nplan/HomeButtons/docs/assets/hb_promo_1.jpeg

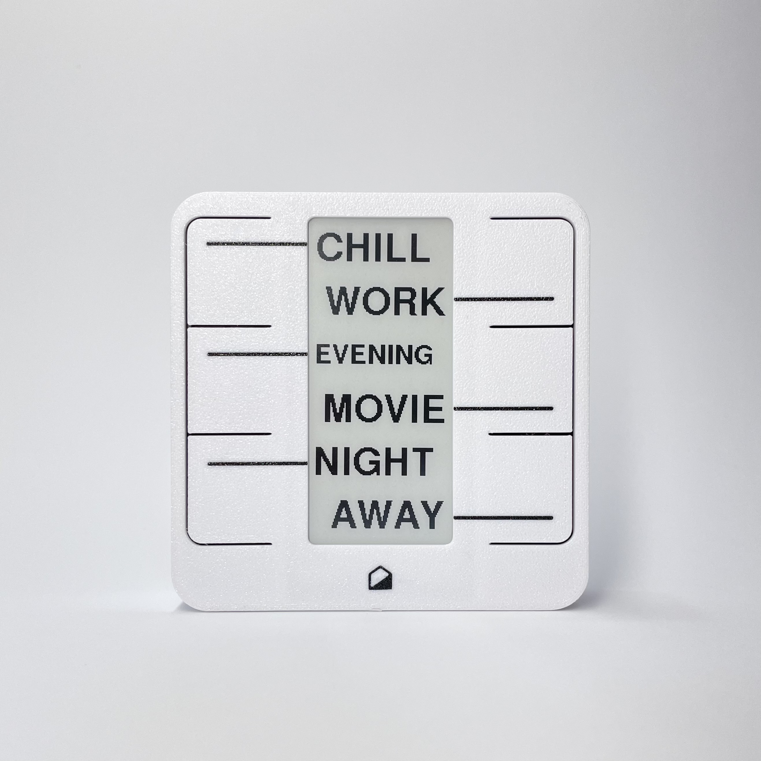
docs/assets/hb_promo_1.jpeg
