nplan/HomeButtons/docs/assets/original_click.gif

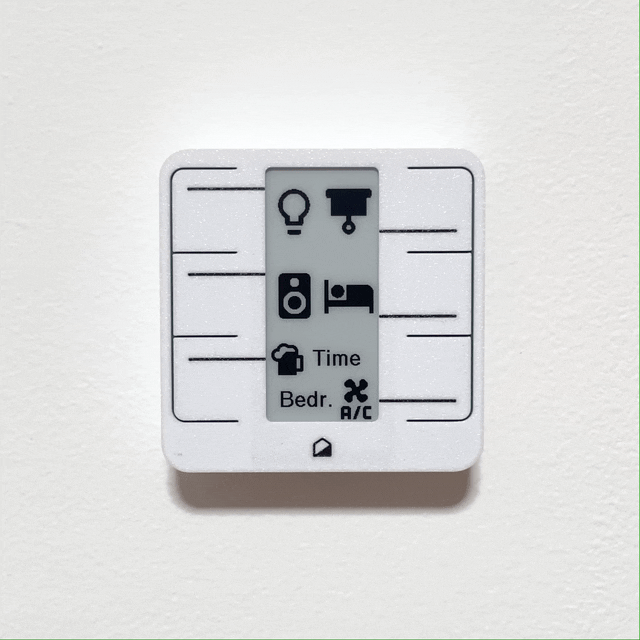
docs/assets/original_click.gif
