nplan/HomeButtons/docs/industrial/assets/button_press.gif

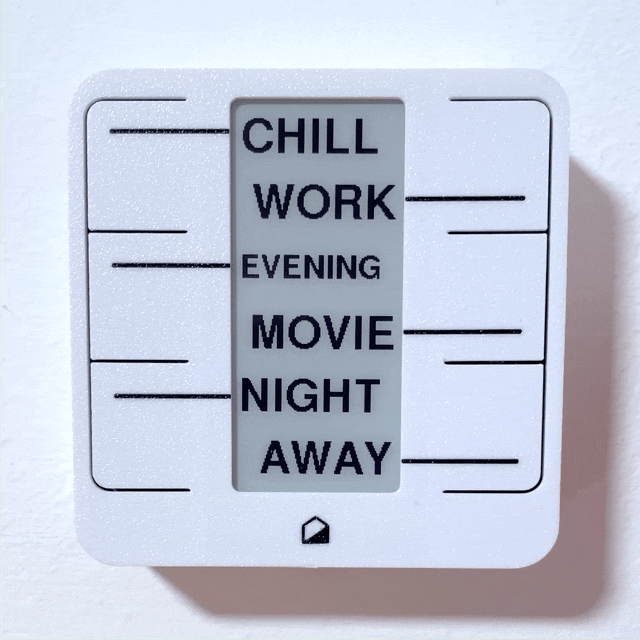
docs/industrial/assets/button_press.gif
