nplan/HomeButtons/docs/industrial/assets/hb_ind_front_iso.png

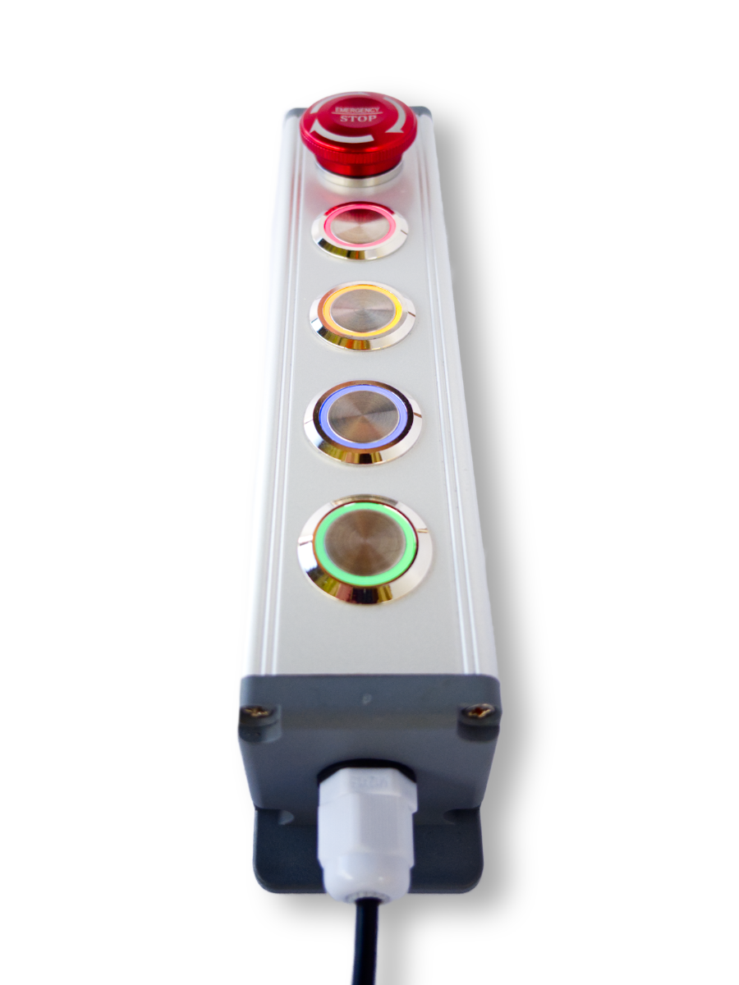
docs/industrial/assets/hb_ind_front_iso.png
