nplan/HomeButtons/docs/industrial/assets/hb_ind_iso.png

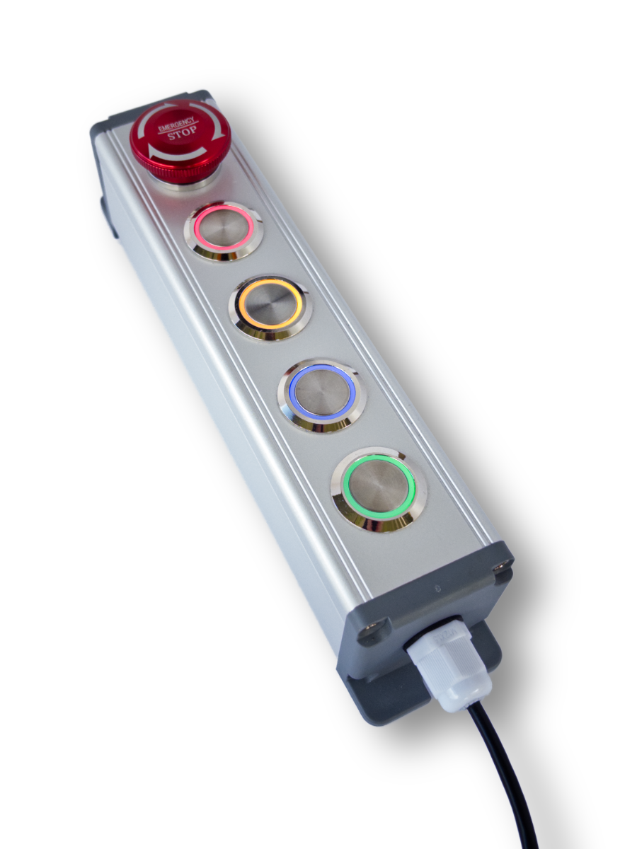
docs/industrial/assets/hb_ind_iso.png
