nplan/HomeButtons/docs/industrial/assets/hb_ind_killswitch_closeup.png

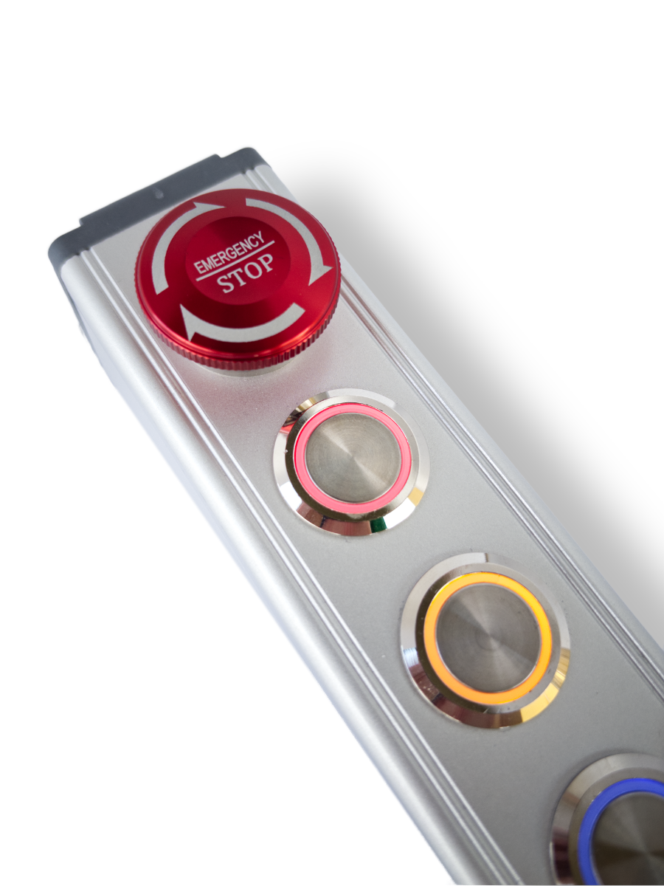
docs/industrial/assets/hb_ind_killswitch_closeup.png
