nplan/HomeButtons/docs/industrial/assets/hb_ind_usb_conn.png

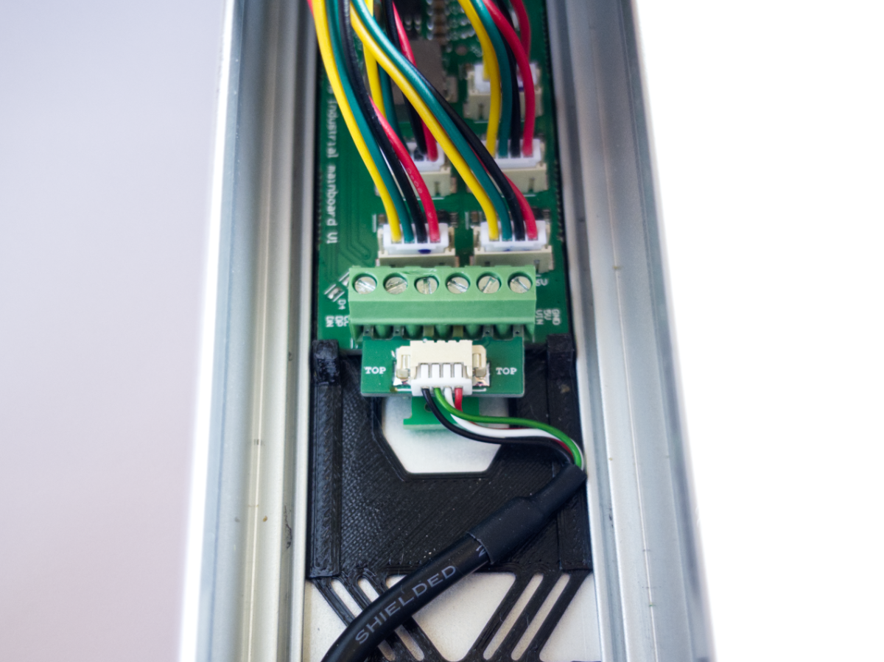
docs/industrial/assets/hb_ind_usb_conn.png
