nplan/HomeButtons/docs/industrial/assets/hb_ind_w_cable.png

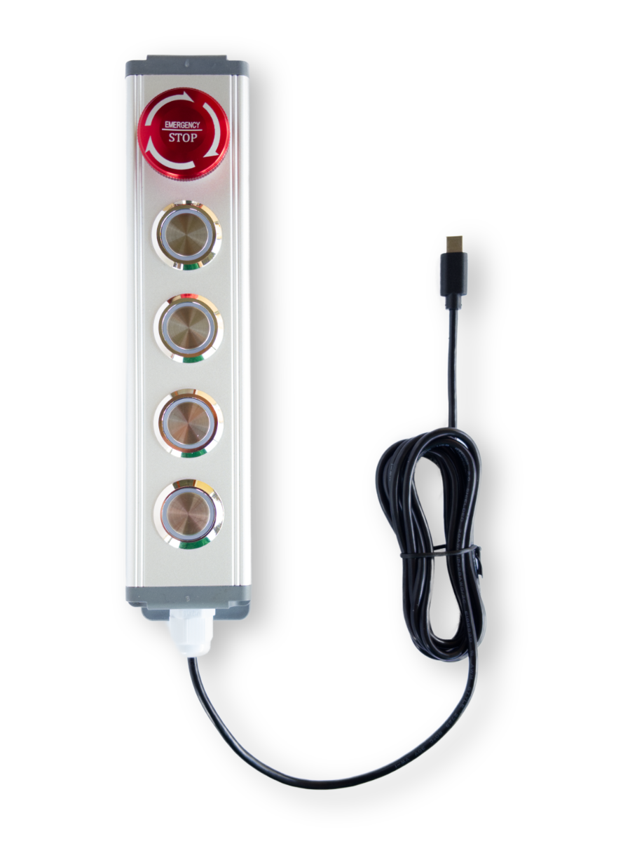
docs/industrial/assets/hb_ind_w_cable.png
