nplan/HomeButtons/docs/industrial/assets/home_buttons_front.jpg

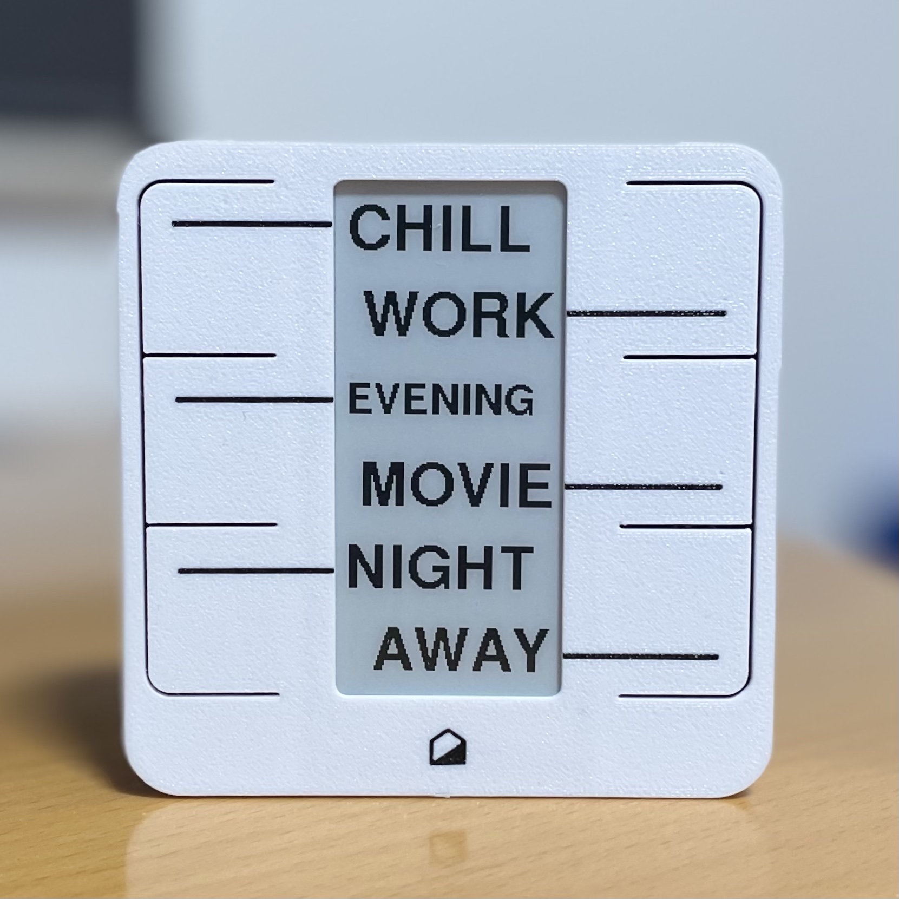
docs/industrial/assets/home_buttons_front.jpg
