nplan/HomeButtons/docs/industrial/assets/mount_2_wall.jpeg

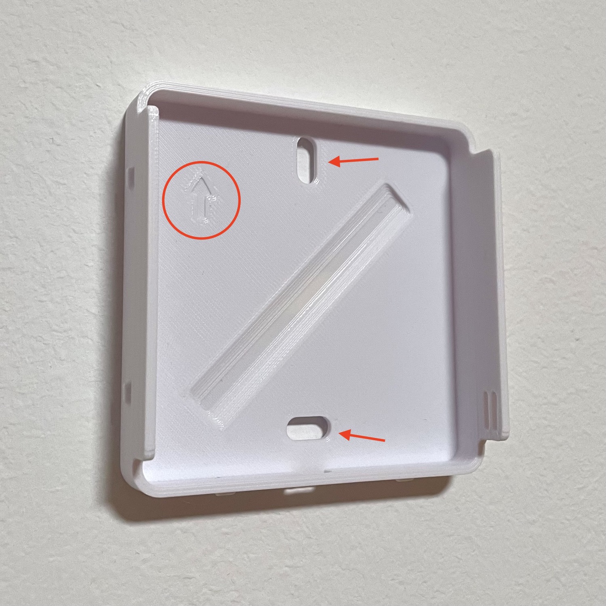
docs/industrial/assets/mount_2_wall.jpeg
