nplan/HomeButtons/docs/industrial/assets/pcb_drawing.png

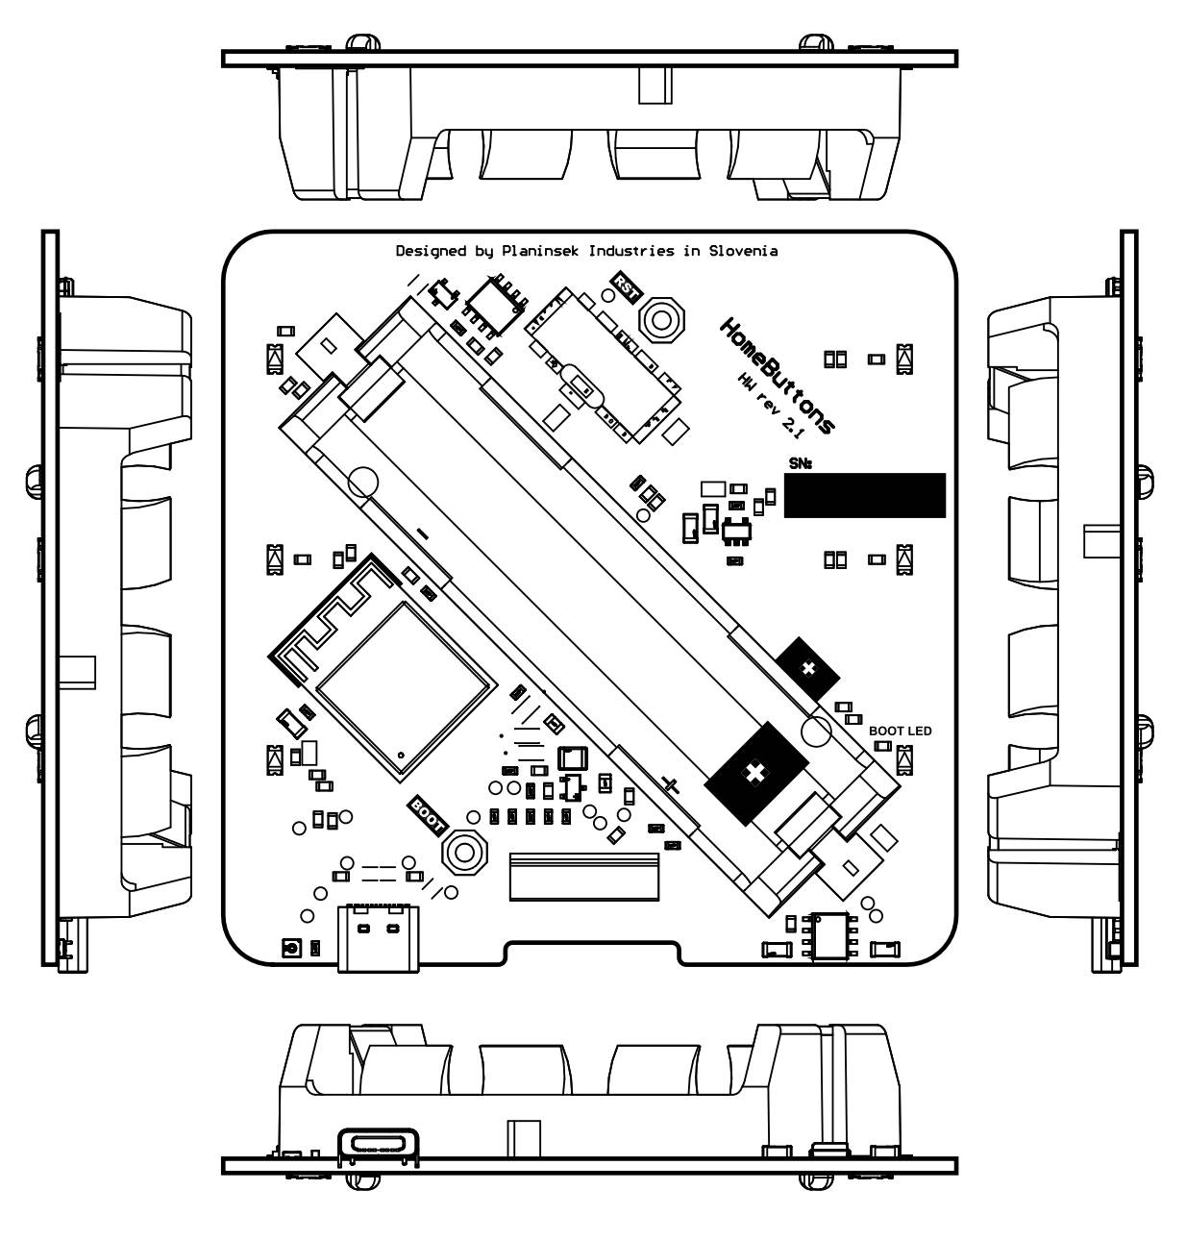
docs/industrial/assets/pcb_drawing.png
