nplan/HomeButtons/docs/industrial/assets/promo_6.gif

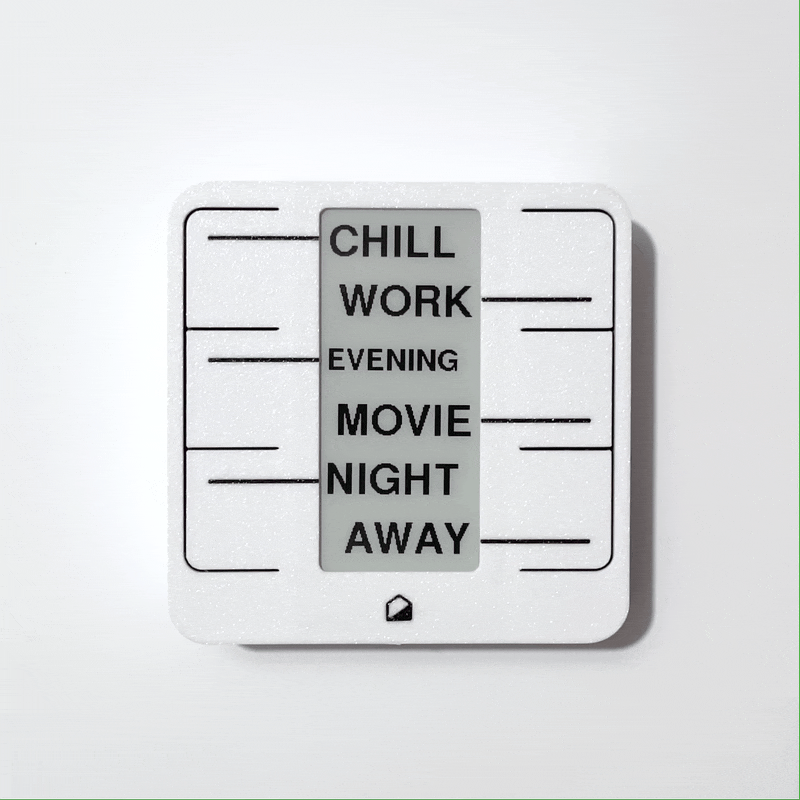
docs/industrial/assets/promo_6.gif
