nplan/HomeButtons/docs/industrial/assets/text_sizes.png

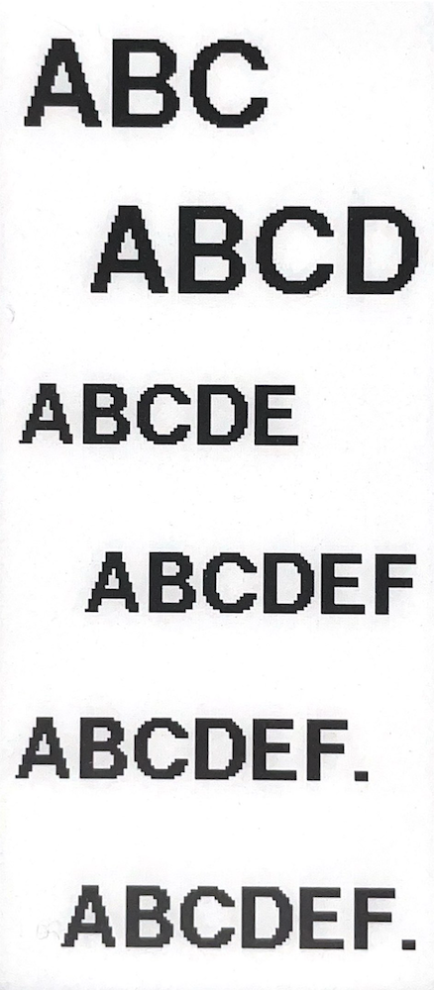
docs/industrial/assets/text_sizes.png
