nplan/HomeButtons/Hardware/PCB/rev_2.3/3D/PCB_dummy_v2.step

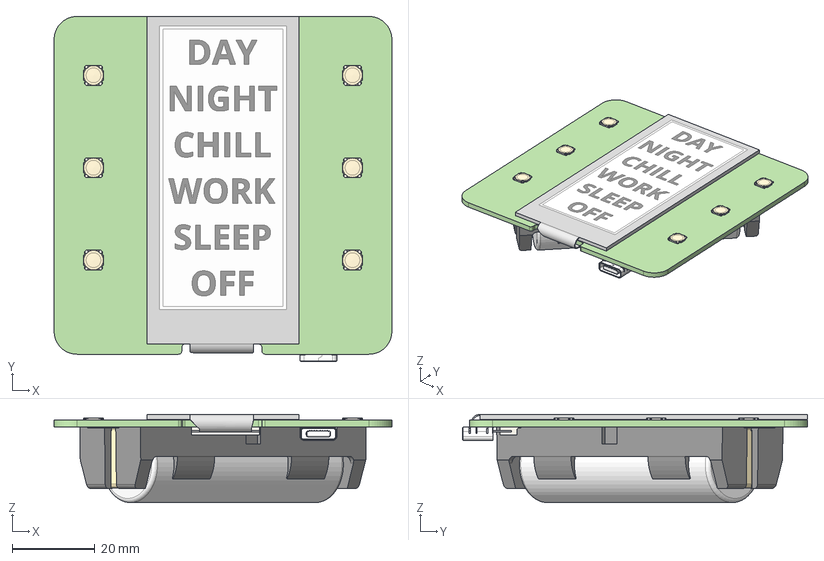
[picture p45: CAD file, 2022-10-29]
Hardware/PCB/rev_2.3/3D/PCB_dummy_v2.step
81.5 x 83.2 x 21.3 mm
SKRBAA x 6
flex connector
PCB dummy
keystone-PN1042
PCB
e-ink GDEY029T94
