nplan/HomeButtons/Hardware/PCB/mini_rev_1.0/3D/HB_mini_PCB_drawing_V0.1.dxf

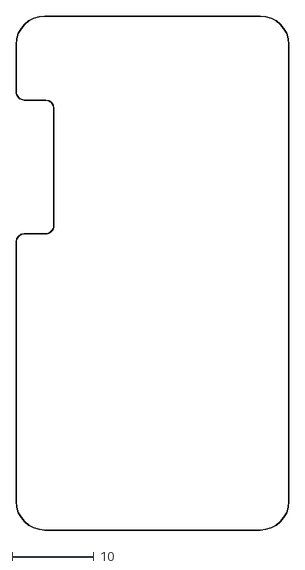
[picture p46: CAD file, 2023-05-28]
Hardware/PCB/mini_rev_1.0/3D/HB_mini_PCB_drawing_V0.1.dxf
33.4 x 63.0
