nplan/HomeButtons/Hardware/PCB/rev_2.3/3D/hbtns dummy v1.step

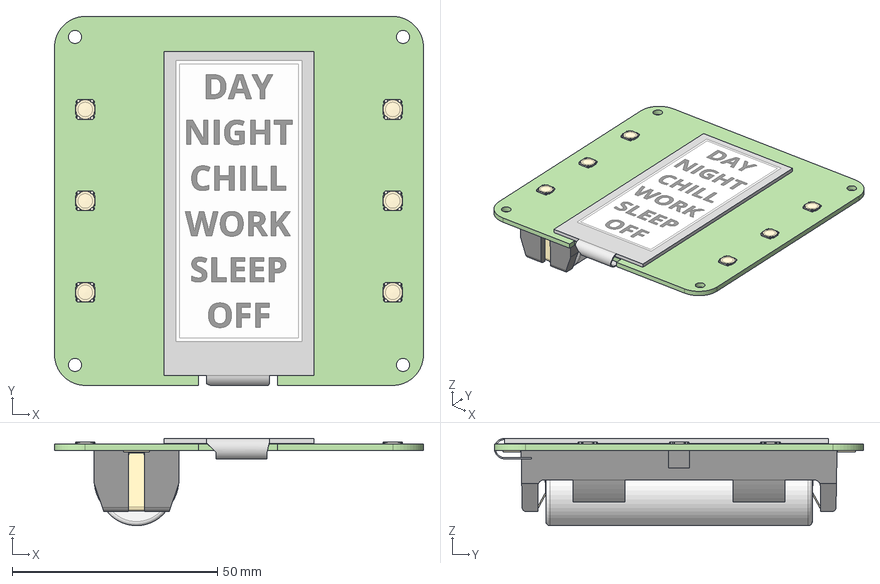
[picture p47: CAD file, 2022-10-29]
Hardware/PCB/rev_2.3/3D/hbtns dummy v1.step
90.0 x 90.0 x 21.3 mm
SKRBAA x 6
e-ink GDEY029T94
PCB dummy
keystone-PN1042
