nplan/HomeButtons/Hardware/PCB/mini_rev_1.0/3D/HB_mini_boardShape_fromOnshape3.dxf.dxf

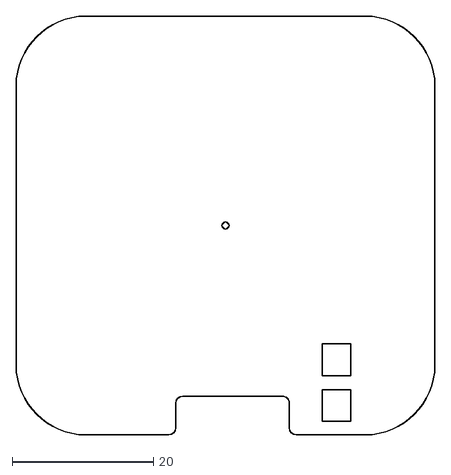
[picture p48: CAD file, 2023-05-28]
Hardware/PCB/mini_rev_1.0/3D/HB_mini_boardShape_fromOnshape3.dxf.dxf
59.4 x 59.4
