nplan/HomeButtons/Hardware/PCB/rev_2.3/3D/e-ink-GDEY029T94-modelV2.step

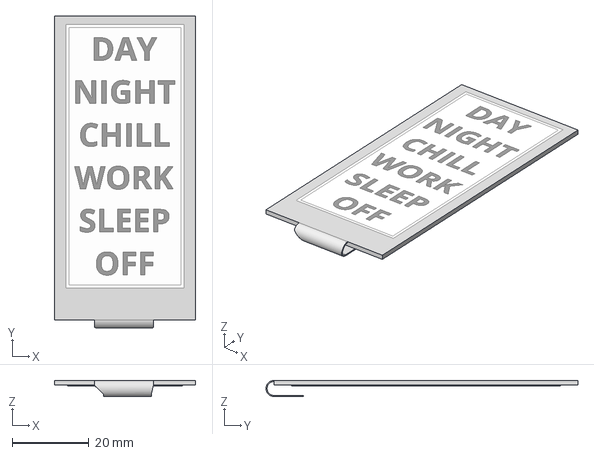
[picture p49: CAD file, 2022-10-29]
Hardware/PCB/rev_2.3/3D/e-ink-GDEY029T94-modelV2.step
36.7 x 81.1 x 4.20 mm
