nplan/HomeButtons/Hardware/PCB/mini_rev_1.0/3D/e-ink GDEY0154D67_nonfoldedFlex.step

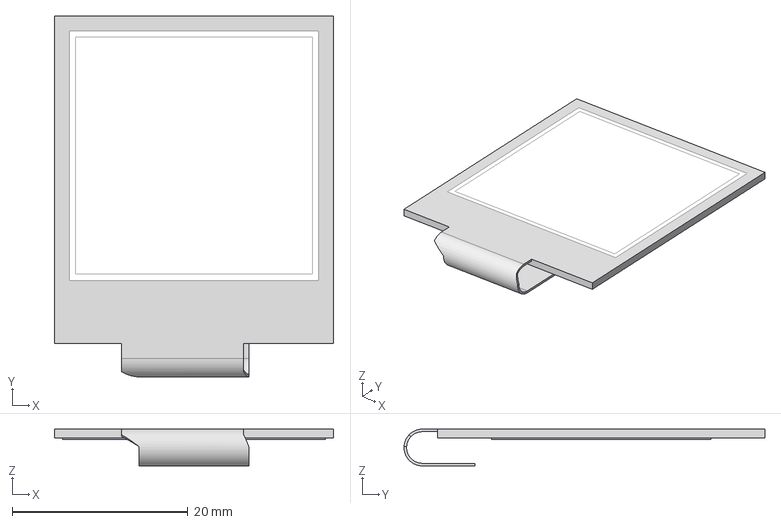
[picture p50: CAD file, 2023-05-28]
Hardware/PCB/mini_rev_1.0/3D/e-ink GDEY0154D67_nonfoldedFlex.step
31.8 x 41.1 x 4.20 mm
