nplan/HomeButtons/Hardware/PCB/rev_2.3/3D/loweffort_con.step

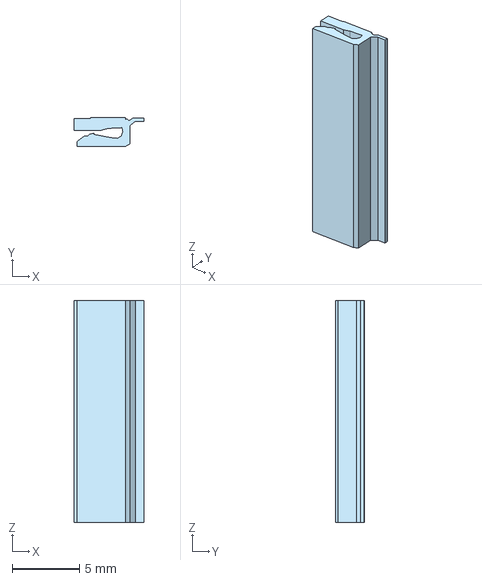
[picture p51: CAD file, 2022-10-29]
Hardware/PCB/rev_2.3/3D/loweffort_con.step
5.22 x 2.12 x 16.5 mm
