nplan/HomeButtons/Firmware/HomeButtonsArduino/include/hardware.h

#ifndef HARDWARE_H
#define HARDWARE_H

#include <Arduino.h>
#include <Wire.h>

#include <semver.hpp>

#include "Adafruit_SHTC3.h"

struct HardwareDefinition {
  semver::version version;

  // ------ PIN definitions ------
  uint8_t BTN1_PIN;
  uint8_t BTN2_PIN;
  uint8_t BTN3_PIN;
  uint8_t BTN4_PIN;
  uint8_t BTN5_PIN;
  uint8_t BTN6_PIN;

  uint8_t LED1_PIN;
  uint8_t LED2_PIN;
  uint8_t LED3_PIN;
  uint8_t LED4_PIN;
  uint8_t LED5_PIN;
  uint8_t LED6_PIN;

  uint8_t SDA;
  uint8_t SCL;
  uint8_t VBAT_ADC;
  uint8_t CHARGER_STDBY;
  uint8_t BOOST_EN;
  uint8_t DC_IN_DETECT;
  uint8_t CHG_ENABLE;

  uint8_t EINK_CS;
  uint8_t EINK_DC;
  uint8_t EINK_RST;
  uint8_t EINK_BUSY;

  // ------ LED analog parameters ------
  uint8_t LED1_CH;
  uint8_t LED2_CH;
  uint8_t LED3_CH;
  uint8_t LED4_CH;
  uint8_t LED5_CH;
  uint8_t LED6_CH;

  uint8_t LED_RES;
  uint16_t LED_FREQ;
  uint8_t LED_BRIGHT_DFLT;

  // ------ battery reading ------
  uint8_t BAT_RES_BITS;
  float BATT_DIVIDER;
  float BATT_ADC_REF_VOLT;
  float MIN_BATT_VOLT;
  float BATT_HISTERESIS_VOLT;
  float WARN_BATT_VOLT;
  float BATT_FULL_VOLT;
  float BATT_EMPTY_VOLT;
  float BATT_PRESENT_VOLT;

  // ------ wakeup ------
  uint64_t WAKE_BITMASK;
};

const HardwareDefinition hw_rev_1_0{// ------ PIN definitions ------
                                    .version = semver::version{1, 0, 0},
                                    .BTN1_PIN = 1,
                                    .BTN2_PIN = 2,
                                    .BTN3_PIN = 3,
                                    .BTN4_PIN = 4,
                                    .BTN5_PIN = 5,
                                    .BTN6_PIN = 6,

                                    .LED1_PIN = 15,
                                    .LED2_PIN = 16,
                                    .LED3_PIN = 17,
                                    .LED4_PIN = 37,
                                    .LED5_PIN = 38,
                                    .LED6_PIN = 45,

                                    .SDA = 10,
                                    .SCL = 11,
                                    .VBAT_ADC = 14,
                                    .CHARGER_STDBY = 12,
                                    .BOOST_EN = 13,

                                    .EINK_CS = 5,
                                    .EINK_DC = 8,
                                    .EINK_RST = 9,
                                    .EINK_BUSY = 7,

                                    // ------ LED analog parameters ------
                                    .LED1_CH = 0,
                                    .LED2_CH = 1,
                                    .LED3_CH = 2,
                                    .LED4_CH = 3,
                                    .LED5_CH = 4,
                                    .LED6_CH = 5,

                                    .LED_RES = 8,
                                    .LED_FREQ = 1000,
                                    .LED_BRIGHT_DFLT = 20,

                                    // ------ battery reading ------“
                                    .BAT_RES_BITS = 12,
                                    .BATT_DIVIDER = 0.5,
                                    .BATT_ADC_REF_VOLT = 2.6,
                                    .MIN_BATT_VOLT = 3.3,
                                    .BATT_HISTERESIS_VOLT = 3.5,
                                    .WARN_BATT_VOLT = 3.5,
                                    .BATT_FULL_VOLT = 4.2,
                                    .BATT_EMPTY_VOLT = 3.3,

                                    // ------ wakeup ------
                                    .WAKE_BITMASK = 0x7E};

const HardwareDefinition hw_rev_2_0{// ------ PIN definitions ------
                                    .version = semver::version{2, 0, 0},
                                    .BTN1_PIN = 5,
                                    .BTN2_PIN = 6,
                                    .BTN3_PIN = 21,
                                    .BTN4_PIN = 1,
                                    .BTN5_PIN = 3,
                                    .BTN6_PIN = 4,

                                    .LED1_PIN = 15,
                                    .LED2_PIN = 16,
                                    .LED3_PIN = 17,
                                    .LED4_PIN = 2,
                                    .LED5_PIN = 38,
                                    .LED6_PIN = 37,

                                    .SDA = 10,
                                    .SCL = 11,
                                    .VBAT_ADC = 14,
                                    .CHARGER_STDBY = 12,
                                    .BOOST_EN = 13,

                                    .EINK_CS = 34,
                                    .EINK_DC = 8,
                                    .EINK_RST = 9,
                                    .EINK_BUSY = 7,

                                    // ------ LED analog parameters ------
                                    .LED1_CH = 0,
                                    .LED2_CH = 1,
                                    .LED3_CH = 2,
                                    .LED4_CH = 3,
                                    .LED5_CH = 4,
                                    .LED6_CH = 5,

                                    .LED_RES = 8,
                                    .LED_FREQ = 1000,
                                    .LED_BRIGHT_DFLT = 100,

                                    // ------ battery reading ------“
                                    .BAT_RES_BITS = 12,
                                    .BATT_DIVIDER = 0.5,
                                    .BATT_ADC_REF_VOLT = 2.6,
                                    .MIN_BATT_VOLT = 3.3,
                                    .BATT_HISTERESIS_VOLT = 3.4,
                                    .WARN_BATT_VOLT = 3.5,
                                    .BATT_FULL_VOLT = 4.2,
                                    .BATT_EMPTY_VOLT = 3.3,

                                    // ------ wakeup ------
                                    .WAKE_BITMASK = 0x20007A};

const HardwareDefinition hw_rev_2_2{// ------ PIN definitions ------
                                    .version = semver::version{2, 2, 0},
                                    .BTN1_PIN = 5,
                                    .BTN2_PIN = 6,
                                    .BTN3_PIN = 21,
                                    .BTN4_PIN = 1,
                                    .BTN5_PIN = 3,
                                    .BTN6_PIN = 4,

                                    .LED1_PIN = 15,
                                    .LED2_PIN = 16,
                                    .LED3_PIN = 17,
                                    .LED4_PIN = 2,
                                    .LED5_PIN = 38,
                                    .LED6_PIN = 37,

                                    .SDA = 10,
                                    .SCL = 11,
                                    .VBAT_ADC = 14,
                                    .CHARGER_STDBY = 12,
                                    .BOOST_EN = 13,
                                    .DC_IN_DETECT = 33,
                                    .CHG_ENABLE = 45,

                                    .EINK_CS = 34,
                                    .EINK_DC = 8,
                                    .EINK_RST = 9,
                                    .EINK_BUSY = 7,

                                    // ------ LED analog parameters ------
                                    .LED1_CH = 0,
                                    .LED2_CH = 1,
                                    .LED3_CH = 2,
                                    .LED4_CH = 3,
                                    .LED5_CH = 4,
                                    .LED6_CH = 5,

                                    .LED_RES = 8,
                                    .LED_FREQ = 1000,
                                    .LED_BRIGHT_DFLT = 100,

                                    // ------ battery reading ------“
                                    .BAT_RES_BITS = 12,
                                    .BATT_DIVIDER = 0.5,
                                    .BATT_ADC_REF_VOLT = 2.6,
                                    .MIN_BATT_VOLT = 3.3,
                                    .BATT_HISTERESIS_VOLT = 3.4,
                                    .WARN_BATT_VOLT = 3.5,
                                    .BATT_FULL_VOLT = 4.2,
                                    .BATT_EMPTY_VOLT = 3.3,
                                    .BATT_PRESENT_VOLT = 2.0,

                                    // ------ wakeup ------
                                    .WAKE_BITMASK = 0x20007A};

const HardwareDefinition hw_rev_2_3{// ------ PIN definitions ------
                                    .version = semver::version{2, 3, 0},
                                    .BTN1_PIN = 5,
                                    .BTN2_PIN = 6,
                                    .BTN3_PIN = 21,
                                    .BTN4_PIN = 1,
                                    .BTN5_PIN = 14,
                                    .BTN6_PIN = 4,

                                    .LED1_PIN = 15,
                                    .LED2_PIN = 16,
                                    .LED3_PIN = 17,
                                    .LED4_PIN = 2,
                                    .LED5_PIN = 38,
                                    .LED6_PIN = 37,

                                    .SDA = 10,
                                    .SCL = 11,
                                    .VBAT_ADC = 3,
                                    .CHARGER_STDBY = 12,
                                    .BOOST_EN = 13,
                                    .DC_IN_DETECT = 33,
                                    .CHG_ENABLE = 45,

                                    .EINK_CS = 34,
                                    .EINK_DC = 8,
                                    .EINK_RST = 9,
                                    .EINK_BUSY = 7,

                                    // ------ LED analog parameters ------
                                    .LED1_CH = 0,
                                    .LED2_CH = 1,
                                    .LED3_CH = 2,
                                    .LED4_CH = 3,
                                    .LED5_CH = 4,
                                    .LED6_CH = 5,

                                    .LED_RES = 8,
                                    .LED_FREQ = 1000,
                                    .LED_BRIGHT_DFLT = 100,

                                    // ------ battery reading ------“
                                    .BAT_RES_BITS = 12,
                                    .BATT_DIVIDER = 0.5,
                                    .BATT_ADC_REF_VOLT = 2.6,
                                    .MIN_BATT_VOLT = 3.3,
                                    .BATT_HISTERESIS_VOLT = 3.4,
                                    .WARN_BATT_VOLT = 3.5,
                                    .BATT_FULL_VOLT = 4.2,
                                    .BATT_EMPTY_VOLT = 3.3,
                                    .BATT_PRESENT_VOLT = 2.0,

                                    // ------ wakeup ------
                                    .WAKE_BITMASK = 0x204072};

// Struct containing current hardware configuration
extern HardwareDefinition HW;

// ------ functions ------
void init_hardware(String hw_version);

void begin_hardware();

bool digitalReadAny();

void set_led(uint8_t ch, uint8_t brightness);

void set_all_leds(uint8_t brightness);

float read_battery_voltage();

uint8_t batt_volt2percent(float volt);

void read_temp_hmd(float &tempe, float &hmd);

bool is_charger_in_standby();

bool is_dc_connected();

void enable_charger(bool enable);

bool is_battery_present();

#endif
