nplan/HomeButtons/Firmware/HomeButtonsArduino/include/config.h

#ifndef CONFIG_H
#define CONFIG_H

#include <Arduino.h>

// ------ device ------
const char MANUFACTURER[] = "PLab";
const char SW_VERSION[] = "v1.1.2";
const char DOCS_LINK[] = "https://docs.home-buttons.com/setup";

// ------ wifi AP ------
const char WIFI_MANAGER_TITLE[] = "Home Buttons";
const char AP_PASSWORD[] = "password123";

// ------ constants ------
const char BTN_PRESS_PAYLOAD[] = "PRESS";
const uint8_t BTN_LABEL_MAXLEN = 15;
const uint8_t MAX_FAILED_CONNECTIONS = 6;
const uint8_t NUM_BUTTONS = 6;

// ------ defaults ------
const char DEVICE_NAME_DFLT[] = "Home Buttons";
const uint16_t MQTT_PORT_DFLT = 1883;
const char BASE_TOPIC_DFLT[] = "homebuttons";
const char DISCOVERY_PREFIX_DFLT[] = "homeassistant";
const char BTN_1_LABEL_DFLT[] = "B1";
const char BTN_2_LABEL_DFLT[] = "B2";
const char BTN_3_LABEL_DFLT[] = "B3";
const char BTN_4_LABEL_DFLT[] = "B4";
const char BTN_5_LABEL_DFLT[] = "B5";
const char BTN_6_LABEL_DFLT[] = "B6";

// ------ sensors ------
const uint16_t SEN_INTERVAL_DFLT = 10; // min
const uint16_t SEN_INTERVAL_MIN = 1; // min
const uint16_t SEN_INTERVAL_MAX = 30; // min

// ----- timing ------
const uint32_t QUICK_WIFI_TIMEOUT = 5000L;
const uint32_t WIFI_TIMEOUT = 15000L;
const uint32_t MQTT_TIMEOUT = 10000L;
const uint32_t SHORT_PRESS_TIME = 100;
const uint32_t MEDIUM_PRESS_TIME = 2000L;
const uint32_t LONG_PRESS_TIME = 10000L;
const uint32_t EXTRA_LONG_PRESS_TIME = 20000L;
const uint32_t ULTRA_LONG_PRESS_TIME = 30000L;
const uint32_t CONFIG_TIMEOUT = 600;  // s
const uint32_t MQTT_DISCONNECT_TIMEOUT = 1000L;
const uint32_t INFO_SCREEN_DISP_TIME = 30000L;  // ms

#endif
