nplan/HomeButtons/Firmware/HomeButtonsArduino/src/bitmaps.h

#ifndef HOMEBUTTONS_BITMAPS_H
#define HOMEBUTTONS_BITMAPS_H

#include <pgmspace.h>

const unsigned char hb_logo_24x24[] PROGMEM = {
    0x00, 0x00, 0x00, 0x00, 0x00, 0x00, 0x00, 0x00, 0x00, 0x00, 0x00, 0x00,
    0x00, 0x3c, 0x00, 0x00, 0x66, 0x00, 0x00, 0xc3, 0x00, 0xc0, 0x00, 0x03,
    0x60, 0x00, 0x06, 0x10, 0x00, 0x08, 0x10, 0x00, 0x0c, 0x10, 0x00, 0x0e,
    0x10, 0x00, 0x0f, 0x10, 0xc0, 0x0f, 0x10, 0xe0, 0x0f, 0x10, 0xf8, 0x0f,
    0x10, 0xfc, 0x0f, 0x10, 0xff, 0x0f, 0x90, 0xff, 0x0f, 0xf0, 0xff, 0x0f,
    0xf0, 0xff, 0x0f, 0x00, 0x00, 0x00, 0x00, 0x00, 0x00, 0x00, 0x00, 0x00};

const unsigned char hb_logo_48x48[] PROGMEM = {
    0x00, 0x00, 0x00, 0x00, 0x00, 0x00, 0x00, 0x00, 0x00, 0x00, 0x00, 0x00,
    0x00, 0x00, 0x00, 0x00, 0x00, 0x00, 0x00, 0x00, 0x00, 0x00, 0x00, 0x00,
    0x00, 0x00, 0x00, 0x00, 0x00, 0x00, 0x00, 0x00, 0x00, 0x00, 0x00, 0x00,
    0x00, 0x00, 0x00, 0x00, 0x00, 0x00, 0x00, 0x00, 0x80, 0x03, 0x00, 0x00,
    0x00, 0x00, 0xe0, 0x07, 0x00, 0x00, 0x00, 0x00, 0xf0, 0x0f, 0x00, 0x00,
    0x00, 0x00, 0x7c, 0x3e, 0x00, 0x00, 0x00, 0x00, 0x3e, 0x7c, 0x00, 0x00,
    0x00, 0x80, 0x0f, 0xf0, 0x01, 0x00, 0x00, 0xc0, 0x07, 0xe0, 0x03, 0x00,
    0x00, 0xf0, 0x01, 0x80, 0x0f, 0x00, 0x00, 0xf8, 0x00, 0x00, 0x1f, 0x00,
    0x00, 0x7c, 0x00, 0x00, 0x3e, 0x00, 0x00, 0x1f, 0x00, 0x00, 0xf8, 0x00,
    0x80, 0x0f, 0x00, 0x00, 0xf0, 0x01, 0x80, 0x07, 0x00, 0x00, 0xe0, 0x01,
    0x80, 0x03, 0x00, 0x00, 0xe0, 0x01, 0x80, 0x03, 0x00, 0x00, 0xf0, 0x01,
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
    0xff, 0xff, 0x00, 0x00, 0x00, 0x00, 0xff, 0xff, 0xff, 0xff, 0x00, 0x00,
    0x00, 0x00, 0xff, 0xff, 0xff, 0xff, 0x00, 0x00, 0x00, 0x00, 0xff, 0xff,
    0xff, 0xff, 0x00, 0x00, 0x00, 0x00, 0xff, 0xff, 0xff, 0xff, 0x00, 0x00,
    0x00, 0x00, 0xff, 0xff, 0xff, 0xff, 0x00, 0x00, 0x00, 0x00, 0xff, 0xff,
    0xff, 0xff, 0x00, 0x00, 0x00, 0x00, 0xff, 0xff, 0xff, 0xff, 0x00, 0x00,
    0x00, 0x00, 0xff, 0xff, 0xff, 0xff, 0x00, 0x00, 0x00, 0x00, 0xff, 0xff,
    0xff, 0xff, 0x00, 0x00, 0x00, 0x00, 0xff, 0xff, 0xff, 0xff, 0x00, 0x00,
    0x00, 0x00, 0xff, 0xff, 0xff, 0xff, 0x00, 0x00, 0x00, 0x00, 0xff, 0xff,
    0xff, 0xff, 0x00, 0x00, 0x00, 0x00, 0xff, 0xff, 0xff, 0xff, 0x00, 0x00,
    0x00, 0x00, 0xfe, 0xff, 0xff, 0x7f, 0x00, 0x00, 0x00, 0x00, 0xf8, 0xff,
    0xff, 0x1f, 0x00, 0x00, 0x00, 0x00, 0x00, 0x00, 0x00, 0x00, 0x00, 0x00,
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

#endif  // HOMEBUTTONS_BITMAPS_H
