nplan/HomeButtons/Firmware/HomeButtonsArduino/src/app.h

#ifndef HOMEBUTTONS_APP_H
#define HOMEBUTTONS_APP_H

#include <array>
#include "state.h"
#include "network.h"
#include "mqtt_helper.h"
#include "topics.h"
#include "logger.h"
#include "hardware.h"
#include "setup.h"

#if defined(HAS_DISPLAY)
#include "display/display.h"
#include "mdi/mdi_helper.h"
#endif

#if defined(HAS_BUTTON_UI)
#include "button_ui/btn_sw_led.h"
#endif

#if defined(HAS_TOUCH_UI)
#include "touch/touch.h"
#endif

class App;

enum class BootCause { RESET, TIMER, BUTTON };

namespace AppSMStates {

class InitState : public State<App> {
 public:
  using State<App>::State;

  void entry() override;

  const char* get_name() override { return "InitState"; }
};

class AwakeModeIdleState : public State<App> {
 public:
  using State<App>::State;

  void entry() override;
  void exit() override;
  void loop() override;
  void handle_ui_event(UserInput::Event event);

  const char* get_name() override { return "AwakeModeIdleState"; }
};

class SleepModeHandleInput : public State<App> {
 public:
  using State<App>::State;

  void entry() override;
  void exit() override;
  void loop() override;
  void handle_ui_event(UserInput::Event event);

  const char* get_name() override { return "SleepModeHandleInput"; }
};

class NetConnectingState : public State<App> {
 public:
  using State<App>::State;

  void entry() override;
  void exit() override;
  void loop() override;
  void handle_ui_event(UserInput::Event event);

  const char* get_name() override { return "NetConnectingState"; }
};

class InfoScreenState : public State<App> {
 public:
  using State<App>::State;

  void entry() override;
  void exit() override;
  void loop() override;
  void handle_ui_event(UserInput::Event event);

  const char* get_name() override { return "InfoScreenState"; }
};

class SettingsMenuState : public State<App> {
 public:
  using State<App>::State;

  void entry() override;
  void exit() override;
  void loop() override;
  void handle_ui_event(UserInput::Event event);

  const char* get_name() override { return "SettingsMenuState"; }
};

class DeviceInfoState : public State<App> {
 public:
  using State<App>::State;

  void entry() override;
  void exit() override;
  void loop() override;
  void handle_ui_event(UserInput::Event event);

  const char* get_name() override { return "DeviceInfoState"; }
};

class CmdShutdownState : public State<App> {
 public:
  using State<App>::State;

  void entry() override;
  void loop() override;

  const char* get_name() override { return "CmdShutdownState"; }
};

class NetDisconnectingState : public State<App> {
 public:
  using State<App>::State;

  void loop() override;

  const char* get_name() override { return "NetDisconnectingState"; }
};

class ShuttingDownState : public State<App> {
 public:
  using State<App>::State;

  void loop() override;

  const char* get_name() override { return "ShuttingDownState"; }
};

class FactoryResetState : public State<App> {
 public:
  using State<App>::State;

  void entry() override;
  void loop() override;

  const char* get_name() override { return "FactoryResetState"; }
};

}  // namespace AppSMStates

using AppStateMachine = StateMachine<
    App, AppSMStates::InitState, AppSMStates::AwakeModeIdleState,
    AppSMStates::SleepModeHandleInput, AppSMStates::NetConnectingState,
    AppSMStates::InfoScreenState, AppSMStates::SettingsMenuState,
    AppSMStates::DeviceInfoState, AppSMStates::CmdShutdownState,
    AppSMStates::NetDisconnectingState, AppSMStates::ShuttingDownState,
    AppSMStates::FactoryResetState>;

class App : public AppStateMachine, public Logger {
 public:
  App();
  App(const App&) = delete;
  void setup();

 private:
#if defined(HAS_SLEEP_MODE)
  void _start_esp_sleep();
  void _go_to_sleep();
#endif
  void _sleep_or_restart();
  std::pair<BootCause, int16_t> _determine_boot_cause();
  void _log_task_stats();
  void _publish_system_state();

  static void _ui_task(void* app);
  void _start_ui_task();

#if defined(HAS_DISPLAY)
  static void _display_task(void* app);
  void _start_display_task();
#endif

  static void _network_task(void* app);
  void _start_network_task();

  void _main_task();
  static void _main_task_helper(void* app) {
    static_cast<App*>(app)->_main_task();
  }

  void _begin_hw();
  void _start_tasks();

  void _handle_ui_event_global(UserInput::Event event);
  void _publish_ui_event(UserInput::Event event);
  void _mqtt_callback(const char* topic, const char* payload);
  void _net_on_connect();
#if defined(HAS_TH_SENSOR)
  void _publish_sensors();
#endif
#if defined(HAS_BATTERY)
  void _publish_battery();
#endif
#if defined(HAS_DISPLAY)
  void _download_mdi_icons();
#endif

#if defined(HAS_AWAKE_MODE)
  void _publish_awake_mode_avlb();
#endif

  DeviceState device_state_;
  TaskHandle_t ui_task_h_ = nullptr;
  TaskHandle_t display_task_h_ = nullptr;
  TaskHandle_t network_task_h_ = nullptr;
  TaskHandle_t main_task_h_ = nullptr;

#if defined(HOME_BUTTONS_ORIGINAL)
  BtnSwLED b1_;
  BtnSwLED b2_;
  BtnSwLED b3_;
  BtnSwLED b4_;
  BtnSwLED b5_;
  BtnSwLED b6_;
  BtnSwLEDInput<NUM_BUTTONS> bsl_input_;
#elif defined(HOME_BUTTONS_MINI)
  BtnSwLED b1_;
  BtnSwLED b2_;
  BtnSwLED b3_;
  BtnSwLED b4_;
  BtnSwLEDInput<NUM_BUTTONS> bsl_input_;
#elif defined(HOME_BUTTONS_INDUSTRIAL)
  BtnSwLED b1_;
  BtnSwLED b2_;
  BtnSwLED b3_;
  BtnSwLED b4_;
  BtnSwLED sw_;
  BtnSwLEDInput<NUM_BUTTONS> bsl_input_;
#endif

#if defined(HAS_TOUCH_UI)
  TouchInput touch_handler_;
#endif

  UserInput::Event user_event_ = {};

#if defined(HAS_DISPLAY)
  MDIHelper mdi_;
  Display display_;
#endif
  TopicHelper topics_;
  Network network_;
  MQTTHelper mqtt_;
  HardwareDefinition hw_;
  HBSetup setup_;

  BootCause boot_cause_;
  uint8_t wakeup_btn_id_ = 0;

  uint32_t last_sensor_publish_ = 0;
  uint32_t last_m_display_redraw_ = 0;
  uint32_t input_start_time_ = 0;
  uint32_t info_screen_start_time_ = 0;
  uint32_t settings_menu_start_time_ = 0;
  uint32_t device_info_start_time_ = 0;
  uint32_t shutdown_cmd_time_ = 0;

  friend class FactoryTest;
  friend class HBSetup;

  friend class AppSMStates::InitState;
  friend class AppSMStates::AwakeModeIdleState;
  friend class AppSMStates::SleepModeHandleInput;
  friend class AppSMStates::NetConnectingState;
  friend class AppSMStates::InfoScreenState;
  friend class AppSMStates::SettingsMenuState;
  friend class AppSMStates::DeviceInfoState;
  friend class AppSMStates::CmdShutdownState;
  friend class AppSMStates::NetDisconnectingState;
  friend class AppSMStates::ShuttingDownState;
  friend class AppSMStates::FactoryResetState;
};

#endif  // HOMEBUTTONS_APP_H
