nplan/HomeButtons/Firmware/HomeButtonsArduino/src/static_string.h

#ifndef HOMEBUTTONS_STATICSTRING_H
#define HOMEBUTTONS_STATICSTRING_H

#include <cstdio>
#include <cstring>
#include <algorithm>
#include "Arduino.h"

// A class to hold a string up to MAX_SIZE characters (or MAX_SIZE+1 characters
// including \0)
template <size_t _MAX_SIZE>
class StaticString {
  static constexpr size_t MAX_SIZE = _MAX_SIZE + 1;  // to include trailing '\0'

 public:
  StaticString() {}
  explicit StaticString(const char* str) {
    auto n = std::snprintf(data_, MAX_SIZE, "%s", str);
    _check_snprintf_return_value(n);
  }

  explicit StaticString(const String& str) {
    auto n = std::snprintf(data_, MAX_SIZE, "%s", str.c_str());
    _check_snprintf_return_value(n);
  }

  template <size_t _OTHER_MAX_SIZE>
  StaticString(const StaticString<_OTHER_MAX_SIZE>& other) {
    auto n = std::snprintf(data_, MAX_SIZE, "%s", other.c_str());
    _check_snprintf_return_value(n);
  }

  template <typename... Args>
  explicit StaticString(const char* format, Args... args) {
    auto n = std::snprintf(data_, MAX_SIZE, format, args...);
    _check_snprintf_return_value(n);
  }

  template <typename... Args>
  void set(Args... args) {
    *this = StaticString(args...);
  }

  const char* c_str() const { return data_; }

  size_t length() const { return strlen(data_); }
  bool empty() const { return strlen(data_) == 0; }
  StaticString substring(size_t i) const { return substring(i, length()); }
  StaticString substring(size_t i, size_t j) const {
    StaticString output;
    if (i > j || i >= length()) {
      return output;
    }
    auto n = std::snprintf(output.data_, std::min(MAX_SIZE, j - i + 1), "%s",
                           data_ + i);
    _check_snprintf_return_value(n);
    return output;
  }

  // removes any leading or trailing spaces
  StaticString trim(void) {
    StaticString output;
    if (empty()) {
      return output;
    }
    auto start = data_;
    while (isspace(*start)) {
      start++;
    }
    auto end = data_ + length() - 1;
    while (end > start && isspace(*end)) {
      end--;
    }
    auto n = std::snprintf(output.data_, static_cast<size_t>(end - start + 2),
                           "%s", start);
    _check_snprintf_return_value(n);
    return output;
  }

  // returns index of first occurrence of c, or -1 if not found
  int index_of(char c, unsigned int start = 0) const {
    if (start >= length()) {
      return -1;
    }
    for (unsigned int i = start; i < length(); i++) {
      if (data_[i] == c) {
        return i;
      }
    }
    return -1;
  }

  char char_at(unsigned int index) const { return operator[](index); }

  void to_upper_case() {
    for (char* p = data_; *p; p++) {
      *p = toupper(*p);
    }
  }

  void to_lower_case() {
    for (char* p = data_; *p; p++) {
      *p = tolower(*p);
    }
  }

  char* begin() { return data_; }
  char* end() { return data_ + length(); }

  template <typename T>
  StaticString operator+(T other) const {
    StaticString output = *this;
    output += other;
    return output;
  }

  template <size_t _OTHER_MAX_SIZE>
  StaticString& operator+=(const StaticString<_OTHER_MAX_SIZE>& other) {
    *this += other.c_str();
    return *this;
  }

  StaticString& operator+=(const String& other) {
    *this += other.c_str();
    return *this;
  }

  StaticString& operator+=(unsigned long i) {
    auto offset = length();
    auto n = std::snprintf(&data_[offset], MAX_SIZE - offset, "%lu", i);
    _check_snprintf_return_value(n);
    return *this;
  }

  StaticString& operator+=(int i) {
    auto offset = length();
    auto n = std::snprintf(&data_[offset], MAX_SIZE - offset, "%d", i);
    _check_snprintf_return_value(n);
    return *this;
  }

  StaticString& operator+=(const char* other) {
    auto offset = length();
    auto n = std::snprintf(&data_[offset], MAX_SIZE - offset, "%s", other);
    _check_snprintf_return_value(n);
    return *this;
  }

  StaticString& operator+=(char other) {
    auto offset = length();
    auto n = std::snprintf(&data_[offset], MAX_SIZE - offset, "%c", other);
    _check_snprintf_return_value(n);
    return *this;
  }

  StaticString& operator=(const char* other) {
    if (!other) {
      data_[0] = '\0';
      return *this;
    }
    auto n = std::snprintf(data_, MAX_SIZE, "%s", other);
    _check_snprintf_return_value(n);
    return *this;
  }

  bool operator==(const char* other) const {
    return std::strncmp(data_, other, MAX_SIZE) == 0;
  }

  template <size_t _OTHER_MAX_SIZE>
  bool operator==(const StaticString<_OTHER_MAX_SIZE> other) const {
    return std::strncmp(data_, other.data_,
                        std::min(MAX_SIZE,
                                 StaticString<_OTHER_MAX_SIZE>::MAX_SIZE)) == 0;
  }

  char operator[](unsigned int i) const {
    if (i >= length()) {
      return '\0';
    }
    return data_[i];
  }

  char& operator[](unsigned int i) {
    static char dummy;
    if (i >= length()) {
      dummy = 0;
      return dummy;
    }
    return data_[i];
  }

 private:
  char data_[MAX_SIZE] = {'\0'};
  void _check_snprintf_return_value(int value) const {
    if (value >= MAX_SIZE)
      ESP_LOGE("static_string",
               "buffer too small (size: %d, wanted: %d, content: %s)", MAX_SIZE,
               value, data_);
    else if (value < 0)
      ESP_LOGE("static_string", "format failed");
  }
};

#endif  // HOMEBUTTONS_STATICSTRING_H
