nplan/HomeButtons/Firmware/HomeButtonsArduino/src/mdi/certificates.h

#ifndef HOMEBUTTONS_CERTIFICATES_H
#define HOMEBUTTONS_CERTIFICATES_H

#include <pgmspace.h>

namespace certificates {

// ISRG Root X1
// https://letsencrypt.org/certificates/
// Valid until: 2030-06-04
const char isrg_root_x1[] PROGMEM = R"CERT(
-----BEGIN CERTIFICATE-----
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
-----END CERTIFICATE-----
  )CERT";

}  // namespace certificates

#endif
