nplan/HomeButtons/Firmware/HomeButtonsArduino/src/mdi/mdi_helper.h

#ifndef HOMEBUTTONS_MDI_HELPER_H
#define HOMEBUTTONS_MDI_HELPER_H

#include <SPIFFS.h>

#include "logger.h"
#include "static_string.h"
#include "state.h"

static constexpr uint8_t MAX_NUM_SIZES = 3;

static constexpr size_t MAX_PATH_LEN = 56;

class MDIHelper : public Logger {
 public:
  MDIHelper(DeviceState& device_state)
      : Logger("MDI"), _device_state(device_state) {}
  bool begin();
  void add_size(uint16_t size);
  bool download(const char* name, uint16_t size);
  bool download(const char* name);
  bool check_connection();
  bool exists(const char* name, uint16_t size);
  bool exists_all_sizes(const char* name);
  File get_file(const char* name, uint16_t size);
  size_t get_free_space();
  bool make_space(size_t size);
  bool remove(const char* name, uint16_t size);
  void end();

 private:
  bool spiffs_mounted_ = false;
  uint16_t sizes_[MAX_NUM_SIZES] = {0};
  uint8_t num_sizes_ = 0;
  StaticString<MAX_PATH_LEN> _get_path(const char* name, uint16_t size);

  DeviceState& _device_state;
};

#endif
