nplan/HomeButtons/Firmware/HomeButtonsArduino/src/types.h

#ifndef HOMEBUTTONS_TYPES_H
#define HOMEBUTTONS_TYPES_H

#include "static_string.h"
#include "config.h"

using SerialNumber = StaticString<8>;
using RandomID = StaticString<6>;
using ModelName = StaticString<30>;
using ModelID = StaticString<2>;
using HWVersion = StaticString<3>;
using UniqueID = StaticString<21>;

using DeviceName = StaticString<20>;
using ButtonLabel = StaticString<BTN_LABEL_MAXLEN>;
using MDIName = StaticString<48>;
using UserMessage = StaticString<USER_MSG_MAXLEN>;
using BtnConfString = StaticString<16>;

using TouchActionString = StaticString<16>;
using ClickActionString = StaticString<16>;

using TopicType = StaticString<MAX_TOPIC_LENGTH>;
using PayloadType = StaticString<MQTT_PYLD_SIZE>;

using SSIDType = StaticString<32>;
using HostnameType = StaticString<32>;

using IconServerType = StaticString<128>;

enum class DisplayPage {
  EMPTY,
  MAIN,
  INFO,
  DEVICE_INFO,
  MESSAGE,
  MESSAGE_LARGE,
  ERROR,
  WELCOME,
  SETTINGS,
  AP_CONFIG,
  WEB_CONFIG,
  TEST
};

struct UIState {
  static constexpr size_t MAX_MESSAGE_SIZE = 64;
  using MessageType = StaticString<MAX_MESSAGE_SIZE>;

  DisplayPage page = DisplayPage::EMPTY;
  MessageType message{};
  MDIName mdi_name{};
  uint16_t mdi_size = 0;
  bool disappearing = false;
  uint32_t appear_time = 0;
  uint32_t disappear_timeout = 0;
};

enum class LabelType : uint8_t { None, Text, Icon, Mixed };

#endif  // HOMEBUTTONS_TYPES_H;
