nplan/HomeButtons/Firmware/HomeButtonsArduino/src/hw_tests.h

#ifndef HOMEBUTTONS_HW_TESTS_H
#define HOMEBUTTONS_HW_TESTS_H

#include <WiFi.h>

#include "hardware.h"
#include "types.h"

class Logger;

namespace hw_tests {
void blink_leds(const Logger& logger, const HWVersion& hw_version);
void led_on_button(const Logger& logger, const HWVersion& hw_version);
void wifi_stress(const Logger& logger, const HWVersion& hw_version);
}  // namespace hw_tests

#endif  // HOMEBUTTONS_HW_TESTS_H
